Allen-Synthesis/EuroPi/software/contrib/bezier-docs/curve-knob.png

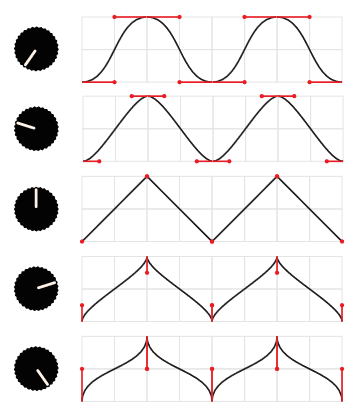
software/contrib/bezier-docs/curve-knob.png
